v9938/ESE_RC755/PCB/PCBwMRAM3.jpg

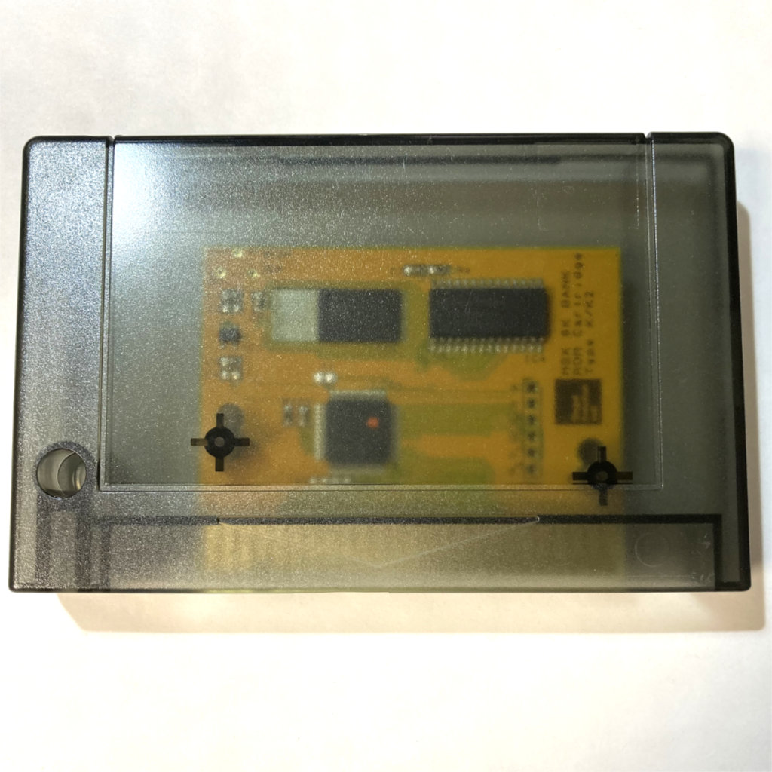
PCB/PCBwMRAM3.jpg
