v9938/ESE_RC755/photo00.jpg

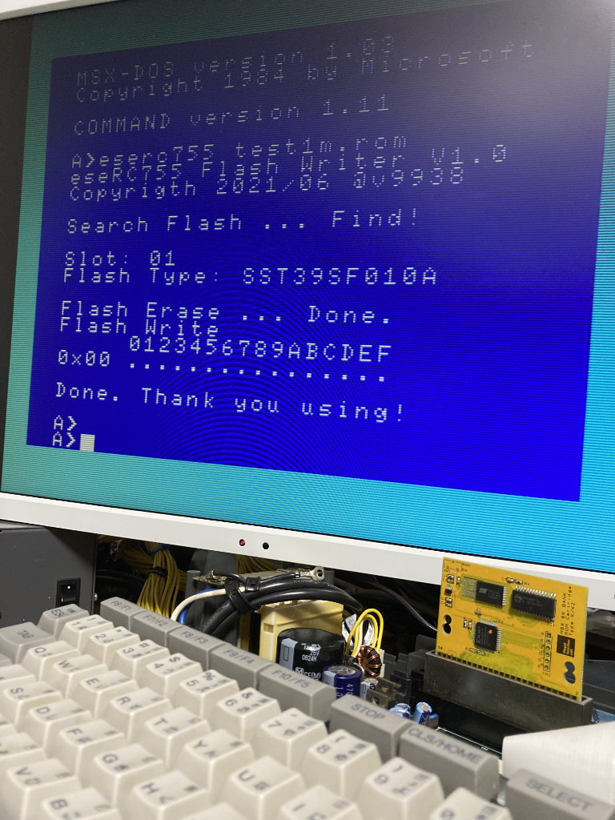
photo00.jpg
